PhilDye/Drum-Lights/RX/src/prototypes.h

#include <FastLED.h>

extern const TProgmemRGBPalette16 WoodFireColors_p FL_PROGMEM = {CRGB::Black, 0x330e00, 0x661c00, 0x992900, 0xcc3700, CRGB::OrangeRed, 0xff5800, 0xff6b00, 0xff7f00, 0xff9200, CRGB::Orange, 0xffaf00, 0xffb900, 0xffc300, 0xffcd00, CRGB::Gold};                      //* Orange
extern const TProgmemRGBPalette16 LithiumFireColors_p FL_PROGMEM = {CRGB::Black, 0x240707, 0x470e0e, 0x6b1414, 0x8e1b1b, CRGB::FireBrick, 0xc14244, 0xd16166, 0xe08187, 0xf0a0a9, CRGB::Pink, 0xff9ec0, 0xff7bb5, 0xff59a9, 0xff369e, CRGB::DeepPink};                 //* Red
extern const TProgmemRGBPalette16 SodiumFireColors_p FL_PROGMEM = {CRGB::Black, 0x332100, 0x664200, 0x996300, 0xcc8400, CRGB::Orange, 0xffaf00, 0xffb900, 0xffc300, 0xffcd00, CRGB::Gold, 0xf8cd06, 0xf0c30d, 0xe9b913, 0xe1af1a, CRGB::Goldenrod};                    //* Yellow
extern const TProgmemRGBPalette16 CopperFireColors_p FL_PROGMEM = {CRGB::Black, 0x001a00, 0x003300, 0x004d00, 0x006600, CRGB::Green, 0x239909, 0x45b313, 0x68cc1c, 0x8ae626, CRGB::GreenYellow, 0x94f530, 0x7ceb30, 0x63e131, 0x4bd731, CRGB::LimeGreen};              //* Green
extern const TProgmemRGBPalette16 AlcoholFireColors_p FL_PROGMEM = {CRGB::Black, 0x000033, 0x000066, 0x000099, 0x0000cc, CRGB::Blue, 0x0026ff, 0x004cff, 0x0073ff, 0x0099ff, CRGB::DeepSkyBlue, 0x1bc2fe, 0x36c5fd, 0x51c8fc, 0x6ccbfb, CRGB::LightSkyBlue};           //* Blue
extern const TProgmemRGBPalette16 RubidiumFireColors_p FL_PROGMEM = {CRGB::Black, 0x0f001a, 0x1e0034, 0x2d004e, 0x3c0068, CRGB::Indigo, CRGB::Indigo, CRGB::Indigo, CRGB::Indigo, CRGB::Indigo, CRGB::Indigo, 0x3c0084, 0x2d0086, 0x1e0087, 0x0f0089, CRGB::DarkBlue}; //* Indigo
extern const TProgmemRGBPalette16 PotassiumFireColors_p FL_PROGMEM = {CRGB::Black, 0x0f001a, 0x1e0034, 0x2d004e, 0x3c0068, CRGB::Indigo, 0x591694, 0x682da6, 0x7643b7, 0x855ac9, CRGB::MediumPurple, 0xa95ecd, 0xbe4bbe, 0xd439b0, 0xe926a1, CRGB::DeepPink};          //* Violet

// 1-8  // solid green, yellow, blue, red, white, cyan, magenta, orange

// 11-18    // green, yellow, blue, red, white, cyan, magenta, orange
// 21-      // bicolor chases
void chase(struct CRGB *targetArray, int numLeds, const struct CRGB &color0, const struct CRGB &color1 = CRGB::Black);

// 50
void fire(struct CRGB *targetArray, int numLeds, const struct CRGBPalette16 &colorPalette);

// 61-      // bicolor twinkles
// 81-88    // single color twinkles (green, yellow, blue, red, white, cyan, magenta, orange)
void colorTwinkle(struct CRGB *targetArray, int numLeds, const struct CRGB &color0, const struct CRGB &color1 = CRGB::Black, const struct CRGB &color2 = CRGB::Black);

// 91-93
void rioSpin(struct CRGB *targetArray, int numLeds);
void rioDisco(struct CRGB *targetArray, int numLeds);
void rioFlag(struct CRGB *targetArray, int numLeds);

// 97
void hazards(struct CRGB *targetArray, int numLeds);

// 98
// strobe

// 99
void rainbow(struct CRGB *targetArray, int numLeds);

// 199 blue strobe
void nineninenine(struct CRGB *targetArray, int numLeds);
